richardhawthorn/SoundMeter/images/DSC_0811.JPG

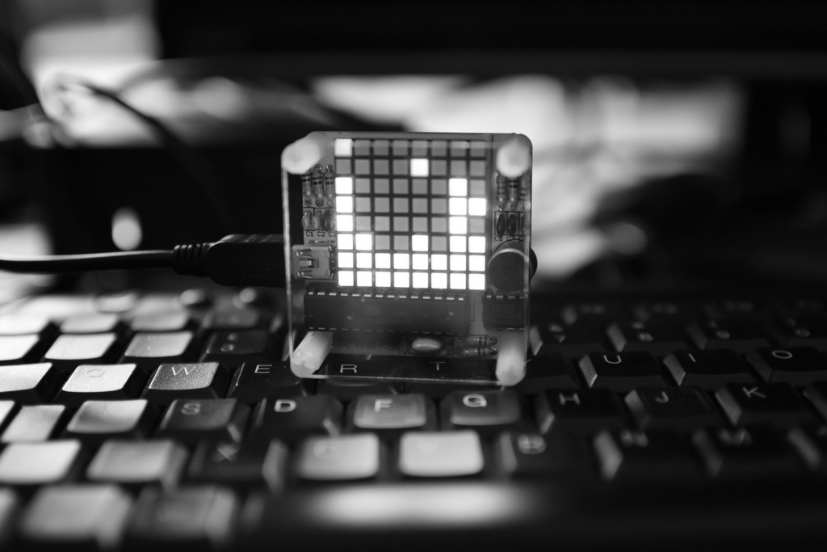
images/DSC_0811.JPG
