richardhawthorn/SoundMeter/images/DSC_0820.JPG

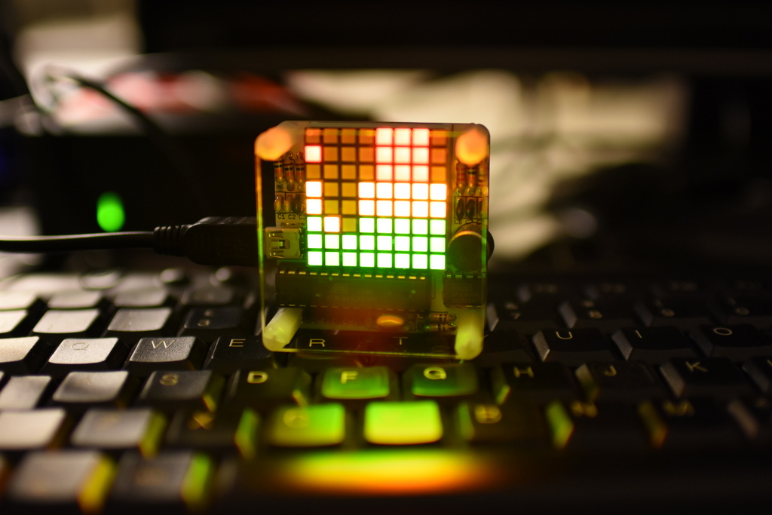
images/DSC_0820.JPG
