richardhawthorn/SoundMeter/images/DSC_5956.JPG

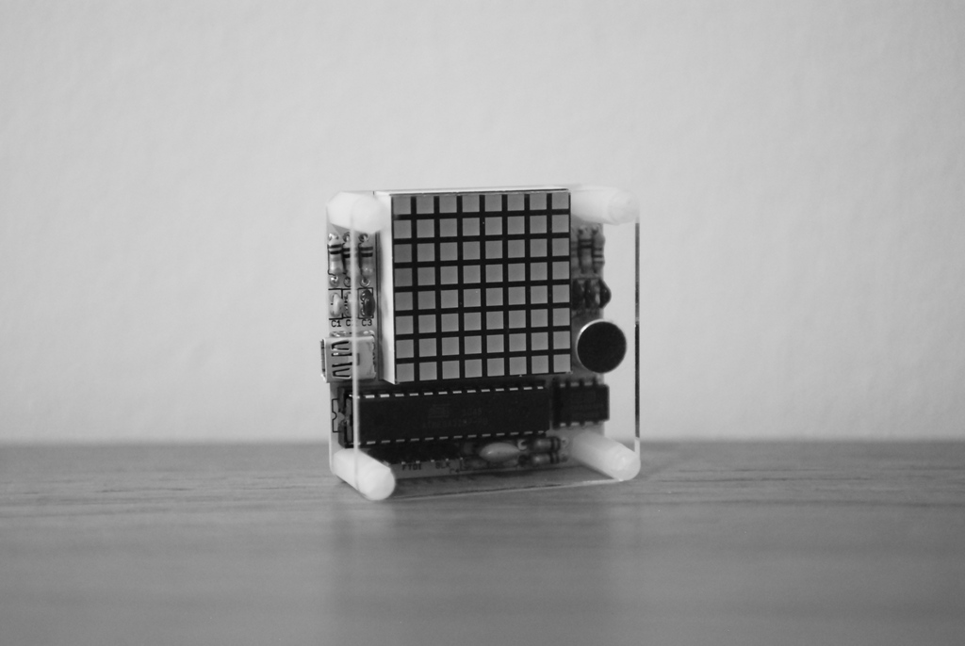
images/DSC_5956.JPG
